heavy-oil1462/hamstra/cad/safe/barrel_holder.scad

// Spare barrel holder: a row of cups for the breech ends, standing on the
// floor of the safe, and a snap clip for each barrel higher up, all from
// one slot layout so every barrel stands plumb.
//
// Barrels are heavy and safe walls are slippery, so the cup row stands
// on the safe floor and carries the weight there: cup floors and back
// plate share one flat bottom. Its magnets only hold it to the wall, and
// the clips only keep the barrels upright.
//
// Barrels differ in length, so by default each clip is its own piece
// with its own plate and magnets, mounted just below its barrel's muzzle
// straight above its cup. clip_row = true joins the clips in one row for
// barrels of about the same length.
//
// Every slot has its own size, wall offset and gap to the next one.
// Per-slot knobs take one entry per slot, or a single value for all (a
// short list repeats its last entry). A size is a diameter, or
// [width, depth] for an oblong item such as an over and under barrel set
// stacked front to back: breech_d = [27, [42, 50]] is a round breech and
// an O/U monoblock, barrel_d = [17.5, [21, 42]] the matching tops. The
// layout is spaced by whichever is bigger per slot, breech or barrel.
//
// Prints as modeled: back plate vertical, cups and rings standing on the
// bed. Pick the part to show or export with `part`; regen_all.py exports
// every option of the dropdown.

include <../design_params.scad>
use <../lib/magnets.scad>
use <../lib/holders.scad>

// Which part to show
part = "cup"; // [cup, clip]

/* [Slots] */
// Breech end size per slot, measured (stands in the cup)
breech_d = [32, 30];
// Barrel size per slot where the clip grips it, measured. Tapered
// barrels: measure where the clip will sit, or mount it just below the
// muzzle and use the muzzle diameter. The clip bore is this times
// clip_fit (design_params.scad): printed rings stretch, so they grip
// well under the barrel size.
barrel_d = [20, 18];
// Extra distance from the safe wall per slot, 0 = tight to the wall
wall_offset = [0, 0];
// Space between neighbouring cups, one entry per pair
gaps = [8];
// Clip position per slot: 0 centered over the cup (round barrels), 1 back
// flush with the cup's back (an O/U set flush with its monoblock's back)
clip_align = [0, 0];
// Clip moved this many mm away from the wall per slot, after clip_align
// (an O/U set standing lump to the wall: back flush plus the lump depth)
clip_shift = [0, 0];

/* [Cup] */
// Cup depth, inside: it only locates the breech, the clip row keeps the
// barrel upright
cup_depth = 25;
// Added to the breech size for the cup. Loose on purpose: the cup only
// locates, and the room lets air around the breech
cup_clearance = 3;
// Cup floor thickness, it carries the barrel onto the safe floor
floor_t = 4.5;
// Drain hole in the floor (0 for none). The cup row stands on the safe
// floor, which blocks a hole: the drain groove is the drain here
drain_d = 0;
// Drain groove in the floor, from under the breech out the front of the
// cup, so moisture runs out and air reaches the breech (0 for none)
groove_w = 4;
// Drain groove depth, leaves floor_t minus this under the groove
groove_d = 2.5;
// Cup back plate height (at least cup depth plus floor)
cup_plate_h = 40;

/* [Clip] */
// Clip ring height
clip_h = 15;
// Clip ring wall, thicker snaps harder
clip_wall = 3;
// Snap opening as a fraction of the clip bore (below 1 snaps)
snap = 0.85;
// Clearance added to the clip bore
clip_clearance = 0.4;
// Clip back plate height
clip_plate_h = 40;
// Join the clips in one row (only for barrels of about the same length)
clip_row = false;

/* [Modular] */
// Print one module per slot, joined side by side with sliding dovetails
modular = false;
// Modular only: 0 lays out every module for printing, 1..n just that one
print_slot = 0;

/* [Friction pad] */
// Show this part's friction pad instead (print in TPU, or use as the
// template to cut silicone sheet; pad_t in design_params.scad)
pad = false;
// The cup row's pad also gets a base pad for under the row, on the safe floor
base_pad = true;

/* [Magnets] */
// Magnet columns on the cup row (the cup row stands on the floor, magnets only hold it to the wall; per module when modular)
magnets_x = 2;
// Magnet columns on the clip row (it only keeps items in)
clip_magnets_x = 2;
// Magnet rows on the cup row
magnets_z = 1;
// Magnet rows on the clip row
clip_magnets_z = 1;

// Slot layout [xs, axes, bounds] for these knobs: the holder uses it, and
// so does the assembly to stand barrels in it.
function barrel_layout(breech_d = breech_d, barrel_d = barrel_d,
                       wall_offset = wall_offset, gaps = gaps,
                       clip_wall = clip_wall, clip_clearance = clip_clearance,
                       clip_align = clip_align, cup_clearance = cup_clearance,
                       clip_shift = clip_shift) =
    let (bd = as_list(breech_d))
    holder_pair_layout([for (d = bd) grow(d, cup_clearance)], wall,
                       [for (i = [0 : len(bd) - 1]) grow(scale_shape(per(barrel_d, i), clip_fit),
                                                           clip_clearance)],
                       clip_wall, gaps, wall_offset, clip_align, clip_shift);

// Height of the cup floor the barrels stand on.
function barrel_floor_t() = floor_t;

// Height of the clip ring, at the bottom of the clip piece.
function barrel_clip_h() = clip_h;

module barrel_holder(part = part, breech_d = breech_d, barrel_d = barrel_d,
                     wall_offset = wall_offset, gaps = gaps,
                     clip_align = clip_align, clip_shift = clip_shift,
                     cup_depth = cup_depth,
                     cup_clearance = cup_clearance, floor_t = floor_t,
                     drain_d = drain_d, groove_w = groove_w, groove_d = groove_d,
                     base_pad = base_pad,
                     cup_plate_h = cup_plate_h,
                     clip_h = clip_h, clip_wall = clip_wall, snap = snap,
                     clip_clearance = clip_clearance,
                     clip_plate_h = clip_plate_h, clip_row = clip_row,
                     magnets_x = magnets_x, clip_magnets_x = clip_magnets_x,
                     magnets_z = magnets_z, clip_magnets_z = clip_magnets_z,
                     modular = modular,
                     print_slot = print_slot, spacing = 12, pad = pad) {
    bd = as_list(breech_d);
    n = len(bd);
    let ($pad = pad) cup_clip_part(part, barrel_layout(breech_d, barrel_d, wall_offset, gaps, clip_wall,
                                      clip_clearance, clip_align, cup_clearance,
                                      clip_shift),
                  [for (d = bd) grow(d, cup_clearance)],
                  [for (i = [0 : n - 1]) grow(scale_shape(per(barrel_d, i), clip_fit), clip_clearance)],
                  cup_depth + floor_t, floor_t, drain_d, 0, cup_plate_h,
                  clip_h, clip_wall, [for (i = [0 : n - 1]) sx(per(barrel_d, i)) * clip_fit * snap],
                  clip_plate_h, clip_row, magnets_x, magnets_z, modular, print_slot,
                  spacing, clip_magnets_x, clip_magnets_z, [groove_w, groove_d], base_pad);
}

barrel_holder();
